Global-Health-Engineering/GHE-data-logger/hardware/design/box_assembly_render2.png

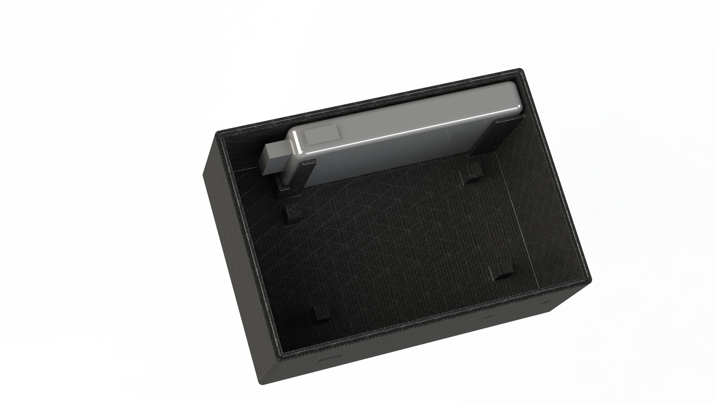
hardware/design/box_assembly_render2.png
